rjrouquette/gpsdo/ltspice/poe.asc

C1: cap; 40µ
C2: cap; 1n
C3: cap; 20µ
C4: cap; 200n
C5: cap; 1n
D1: schottky; RB068LAM100
D7: zener; BZX84C12L
L1: ind2; 18µ; Rser=90m
L2: ind2; 18µ; Rser=90m
L3: ind2; 21.6µ; Rser=90m
L4: ind2; 21.6µ; Rser=90m
M1: nmos; BSC340N08NS3
Q1: pnp; 2N3906
Q2: pnp; 2N3906
Q3: npn; 2N3904
Q4: npn; 2N3904
Q5: npn; 2N3904
Q6: npn; 2N3904
Q7: npn; 2N3904
Q8: pnp; 2N5401
Q9: pnp; 2N3906
Q10: npn; 2N3904
Q11: npn; 2N3904
Q12: npn; 2N3904
R1: res; 10k
R2: res; 150k
R3: res; 3k
R4: res; 3k
R5: res; 10
R6: res; 750m
R7: res; 1k
R8: res; 3k
R9: res; 2.5k
R10: res; 1k
R11: res; 150k
R12: res; 330
R13: res; 10k
R14: res; 1k
R15: res; 10k
U2: LT1634-2.5
U3: 4N25
V1: voltage; 48; Rser=1
Named nets: 0, VPOE, out
.tran 100m startup
K1 L1 L2 L3 L4 0.999
.TEMP 40
